EmilianoBruni/at-me/Releases/00.02/pcb.png

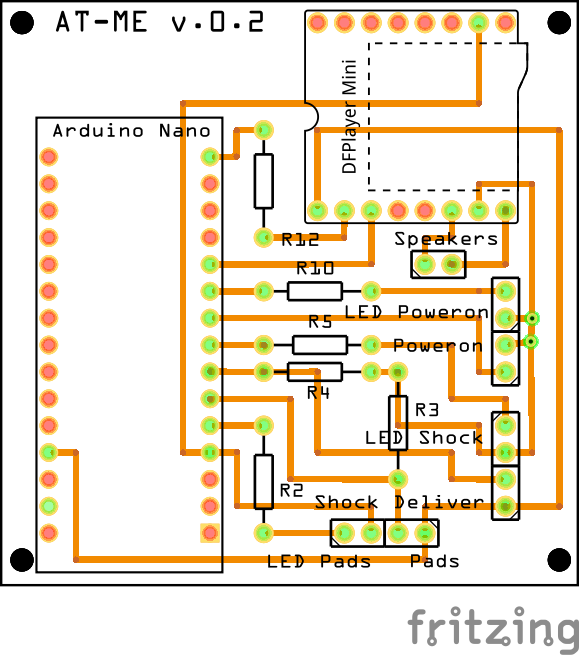
Releases/00.02/pcb.png
